demianmozo/amp_AB/LTSpice/amplificador_completo.asc

C1: cap; 470n; Rser=0 Lser=0 mfg="Murata" pn="GRM033R61C104KE14" type="X5R"
C2: polcap; 470µ; Rser=8.7m Lser=7.838n mfg="Würth Elektronik" pn="870135375007 WCAP-PTHT 10 x 12,5" type="Al polymer"
C3: polcap; 1m; Rser=86m Lser=26.8n mfg="Würth Elektronik" pn="860020475018 WCAP-ATG5 10x20" type="Al electrolytic"
C4: cap; 1n; Rser=0 Lser=0 mfg="Murata" pn="GRM1555C1H102JA01" type="C0G"
R1: res; 12
R2: res; 6.8k
R3: res; 100k
R4: res; 100k
tip141: npn
tip146: pnp
U1: opamp2; NE5532
V1: voltage; -19
V2: voltage; 19
V3: voltage; SINE(1 1 15k); AC 1 0
Named nets: 0, Vo, Vi
.tran 0 1m 0 10u
.lib todo.lib
.ac dec 100 10 100k
